andreeaudateanu/TSC_EBookReader-Project/Images/DeviceOpened.png

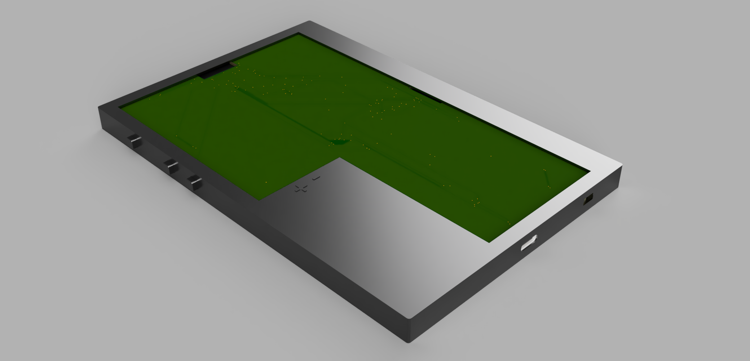
Images/DeviceOpened.png
