andreeaudateanu/TSC_EBookReader-Project/Images/E-BookReader3DExpanded.png

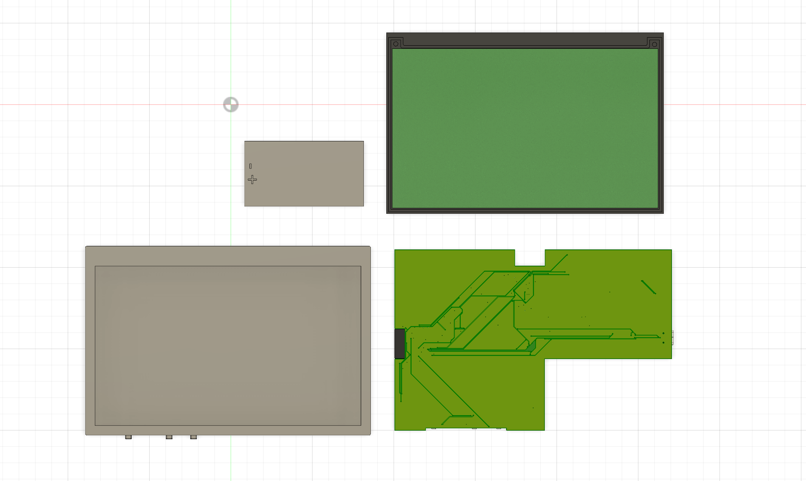
Images/E-BookReader3DExpanded.png
